DanForever/PCRemote/data/images/loading.gif

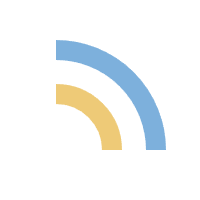
data/images/loading.gif
